CaryXiao1/cs140e-lightsaber/i2c/mpu-6050.c

// engler: simplistic mpu6050 driver code.
//
// we smash all the code in here so its easy to find in the lab
// setting: when it works, seperate it out!
//
// three parts:
//  1. i2c helpers (you don't have to modify)
//  2. accel routines (you have to finish)
//  3. gyro routines (you have to finish)
//
// two algorithms: 
//   - implement the code from scratch (fun! let us know you're
//     doing)
//   - grep for TODO and fill in.
//
// KEY: document why you are doing what you are doing.
//  **** put page numbers for any device-specific things you do ***
//  **** put page numbers for any device-specific things you do ***
//  **** put page numbers for any device-specific things you do ***
//  **** put page numbers for any device-specific things you do ***
//  **** put page numbers for any device-specific things you do ***
//  **** put page numbers for any device-specific things you do ***
//  **** put page numbers for any device-specific things you do ***
// 
// also: a sentence or two will go a long way in a year when you want 
// to re-use the code.
#include "rpi.h"
#include "mpu-6050.h"

/**********************************************************************
 * 1. i2c helpers (see i2c.h)  for reading and write individual registers,
 * and for doing burst reads of N registers.
 *
 * recall: each register has a 1 byte name and a 1 byte value.  we
 * read or write them explicitly using i2c rather than using memory
 * loads and stores (as we do with broadcom memory mapped device 
 * interfaces).
 *
 * you don't have to modify this.
 */

// read a single device register <reg> from i2c device 
// <addr> and return the result.
uint8_t imu_rd(uint8_t addr, uint8_t reg) {
    i2c_write(addr, &reg, 1);
    uint8_t v;
    i2c_read(addr,  &v, 1);
    return v;
}

// set a single device register <reg> on device
// <addr> to value <v>
// 
// the operation is sent over i2c as two 8-bit values: 
// (byte 0 = <reg>, byte 1 = <v>)
void imu_wr(uint8_t addr, uint8_t reg, uint8_t v) {
    uint8_t data[2];
    data[0] = reg;
    data[1] = v;
    i2c_write(addr, data, 2);
}

// do a "burst read" of <n> registers into buffer <v>, where 
//  - <addr> = device addr
//  - <base_reg> = lowest reg in sequence
//  - <n> = total number of 8-bit registers to read.
int imu_rd_n(uint8_t addr, uint8_t base_reg, uint8_t *v, uint32_t n) {
    i2c_write(addr, (void*) &base_reg, 1);
    return i2c_read(addr, v, n);
}

/**********************************************************************
 * 2. simple accel setup and use
 */

// IMU + accel register map
enum {
    // p6, p14
    accel_config_reg = 0x1c,
    accel_off = 3,

    USER_CTRL = 0x6a,   // p 39

    // p31,32
    ACCEL_XOUT_H = 0x3b,
    accel_xout_l = 0x3c,
    accel_yout_h = 0x3d,
    accel_yout_l = 0x3e,
    accel_zout_h = 0x3f,
    accel_zout_l = 0x40,

    // p 41
    PWR_MGMT_1 = 0x6b,
    // p 42
    PWR_MGMT_2 = 108,

    // p 29
    INT_STATUS = 0x3a,
    // p 28
    INT_ENABLE = 0x38,

    // NOTE: p 27, for interrupts
    INT_PIN_CFG = 0x37, 
};

// returns a scaled milligauss value given the
// scale that <g> can range over.
static int mg_scaled(int v, int g) {
    return (v * 1000 * g) / SHRT_MAX;
}

// takes in raw data and scales it.
imu_xyz_t accel_scale(accel_t *h, imu_xyz_t xyz) {
    int g = h->g;
    int x = mg_scaled(h->g, xyz.x);
    int y = mg_scaled(h->g, xyz.y);
    int z = mg_scaled(h->g, xyz.z);
    return xyz_mk(x,y,z);
}

// check interrupt status (INT_STATUS) to see 
// if data is ready.
// 
// extension: hook up gpio interrupts and 
// pull the reading into a circular buffer
// (similar to device lab).
int accel_has_data(const accel_t *h) {
    // pg. 29 of reg map, see DATA_RDY_INT at bit 0
    char reg = imu_rd(h->addr, INT_STATUS);
    return bit_is_on(reg, 0);
}


// combines a 8-bit <lo> and 8-bit <hi> from the sensor into
// a single *signed* 16-bit value.  you want to make sure that
// if the 16-th bit is set, the returned value will be negative.
// i'd suggest playing w/ gdb or small C programs to see that what
// C does matches your intuition.
static short mg_raw(uint8_t lo, uint8_t hi) {
    short out = 0; 
    out |= lo; 
    out |= hi << 8; 
    return out;
}

// sanity testing code.
static void test_mg(int expected, uint8_t l, uint8_t h, unsigned g) {
    int s_i = mg_scaled(mg_raw(h,l),g);

    output("expect = %d, got %d", expected, s_i);
    if(expected == s_i)
        output("success!\n");
    else
        output("failed!\n");

    assert(s_i == expected);
}
    
// set to accel 2g (p14), bandwidth 20hz (p15)
// https://stackoverflow.com/questions/60419390/mpu-6050-correctly-reading-data-from-the-fifo-register
    accel_t mpu6050_accel_init(uint8_t addr, unsigned accel_g) {
        unsigned g = 0;
    switch(accel_g) {
    case accel_2g: g = 2; break;
    case accel_4g: g = 4; break;
    case accel_8g: g = 8; break;
    case accel_16g: g = 16; break;
    default: panic("invalid g=%b\n", g);
    }

    // first test that your scaling works.
    // this is device independent.
    test_mg(0, 0x00, 0x00, 2);
    test_mg(350, 0x16, 0x69, 2);
    test_mg(1000, 0x40, 0x09, 2);
    test_mg(-350, 0xe9, 0x97, 2);
    test_mg(-1000, 0xbf, 0xf7, 2);

    // initialized your accel to 2g (accel_confi_reg)
    uint8_t accel_config = imu_rd(addr, accel_config_reg); 
    accel_config &= ~(0b11 << 3); 
    // accel_config = bits_set(accel_config, 3, 4, accel_g);  
    imu_wr(addr, accel_config_reg, accel_config);
    // todo("setup accel with 2g");

    output("accel_config_reg=%b\n", imu_rd(addr, accel_config_reg));
    return (accel_t) { .addr = addr, .g = g, .hz = 20 };
}

// hard reset: recall --- for all external devices connected to 3v or 
// 5v, rebooting the pi has no effect on the external device.  so either
// we would have to disconnect/reconnect the power (manually or w/ some
// transistor) or we can use the device control to do a hard reset.  we
// do the latter.
void mpu6050_reset(uint8_t addr) {
    // make sure device is up.
    delay_ms(100);

    // page 41: to reset device: set bit 7 = 1 in register
    // PWR_MGMT_1 (register 0x6b)
    // todo("reset device");
    uint8_t pwr_mgmt_reg = imu_rd(addr, PWR_MGMT_1); 
    pwr_mgmt_reg = pwr_mgmt_reg | (1 << 7); // page 42; resets all internal registers to default values
    imu_wr(addr, PWR_MGMT_1, pwr_mgmt_reg); 

    // TODO: See Section 3 for default values

    // XXX: we should read different registers and see that they
    // went back to startup.

    // give time to shutdown, spin up.
    delay_ms(100);

    if(bit_is_on(imu_rd(addr, PWR_MGMT_1), 6))
        output("device booted up in sleep mode!\n");

    // clear sleep mode: (PWR_MGMT_1)
    // if you do *NOT* do this, then the device we have does not work.
    // according to my reading of the data sheet, the value of 0x6b should
    // be 0 after reset.  so i don't get this.
    // todo("clear sleep mode");
    pwr_mgmt_reg = imu_rd(addr, PWR_MGMT_1); // Had to read again
    pwr_mgmt_reg = bit_clr(pwr_mgmt_reg, 6); // pg. 42
    imu_wr(addr, PWR_MGMT_1, pwr_mgmt_reg); // put back in memory

    delay_ms(100);

    // page 39: USER_CTRL (register 0x6a): reset:
    //   - the signal path 
    //   - i2c master mode 
    //   - fifo
    // not sure if redundant after device reset --- datasheet
    // unclear --- so we do to be sure.
    // todo("reset all these");
    uint8_t usr_ctrl_reg = imu_rd(addr, USER_CTRL); 
    usr_ctrl_reg = bits_set(usr_ctrl_reg, 0, 2, 0b111); // the signal path
    imu_wr(addr, USER_CTRL, usr_ctrl_reg); 

    delay_ms(100);

    // NOTE: enable interrupts only on the IMU, not on your pi.
    // (INT_ENABLE) after you config (p27):
    // - latch to be held high until cleared;
    // - read to clear it.
    uint8_t int_pin_cfg_reg = imu_rd(addr, INT_PIN_CFG); 
    int_pin_cfg_reg = bit_set(int_pin_cfg_reg, 4); 
    int_pin_cfg_reg = bit_set(int_pin_cfg_reg, 5); // NOTE: questionable
    imu_wr(addr, INT_PIN_CFG, int_pin_cfg_reg); 

    uint8_t int_enable_reg = imu_rd(addr, INT_ENABLE); 
    int_enable_reg = bit_set(int_enable_reg, 0);  // data ready interrupt
    // int_enable_reg = bit_set(int_enable_reg, 3); 
    // int_enable_reg = bit_set(int_enable_reg, 4); 
    // int_enable_reg = bit_set(int_enable_reg, 6); 
    imu_wr(addr, INT_ENABLE, int_enable_reg); 
    // todo("enable IMU interrupts so you can tell that data is ready");
}

// block until there is data and then return it (raw)
//
// p26 interprets the data.
// if high bit is set, then result is negative.
//
// read them all at once for consistent
// readings using autoincrement.
imu_xyz_t accel_rd(const accel_t *h) {
    uint8_t addr = h->addr;
    uint8_t regs[6];

    // wait until data.
    while(!accel_has_data(h))
        ;

    // read in from the IMU using imu_rd_n.
    //
    // NOTE: from page 32: the "high" byte has a register 
    // value *smaller than* the "low" byte.
    //
    //      xout[15:8] = 0x3b
    //      xout[7:0]  = 0x3c
    //      yout[15:8] = 0x3d
    //      yout[7:0]  = 0x3e
    //      zout[15:8] = 0x3f
    //      zout[7:0]  = 0x40

    // return a raw xyz point.
    int x =  0;
    int y =  0;
    int z =  0;

    // NOTE:
    //  - if this doesn't work, read regs one at a time.
    //  - you'll have to comine the two 8-bit unsigned
    //    regs into a signed 16 bit number using <mg_raw>
    uint8_t v[6]; 
    imu_rd_n(addr, ACCEL_XOUT_H, v, 6);
    
    // combine to get values
    x = mg_raw(v[1], v[0]); 
    y = mg_raw(v[3], v[2]); 
    z = mg_raw(v[5], v[4]); 
    // todo("implement burst reads and return as unscaled x,y,z");
    
    return xyz_mk(x,y,z);
}

/*********************************************************************
 * gyro code
 * 
 * don't trust the scaling  code.
 */

// gyro registers.
enum {
    // p13, p6
    CONFIG = 28, 
    // p14, p6
    GYRO_CONFIG = 29, 

    // p6, p14
    gyro_config_reg = 0x1b,

    // p7
    GYRO_XOUT_H = 67,
};

static inline int 
mdps_scaled(int x, int dps_scale) {
    return (x * dps_scale) / 1000;
}

// not sure this is right: use the code below?
imu_xyz_t gyro_scale(gyro_t *h, imu_xyz_t xyz) {
    int dps = h->dps;
    int x = mdps_scaled(dps, xyz.x);
    int y = mdps_scaled(dps, xyz.y);
    int z = mdps_scaled(dps, xyz.z);
    return xyz_mk(x,y,z);
}

// not sure this is right.
static int dps_to_scale(unsigned dps) {
    switch(dps) {
    // we do this just for testing.
    case 245:
    case 250:  return  8750;
    case 500:  return 17500;
    case 1000: return 35000;
    case 2000: return 70000;
    default: panic("invalid dps: %d\n", dps);
    }
}

// not sure this is right.
static int mdps_scale_deg2(int deg, int dps) {
    // hack to get around no div
    if(dps == 250)
        return (deg * 250) / SHRT_MAX;
    else if(dps == 500)
        return (deg * 500) / SHRT_MAX;
    else
        panic("bad dps=%d\n", dps);
}

// not sure this is right.
static int mdps_scale_deg(int deg, int dps) {
    return (deg * dps_to_scale(dps)) /1000;
}

static inline int within(int exp, int have, int tol) {
    int diff = exp - have;
    if(diff < 0)
        diff = -diff;
    return diff <= tol;
}

static void test_dps(int expected_i, uint8_t h, uint8_t l, int dps) {
    int s_i = mdps_scale_deg(mg_raw(l, h), dps);
    expected_i *= 1000;
    int tol = 5;
    if(!within(expected_i, s_i, tol))
        panic("expected %d, got = %d, scale=%d\n", expected_i, s_i, dps);
    else
        output("expected %d, got = %d, (within +/-%d) scale=%d\n", expected_i, s_i, tol, dps);
}

gyro_t mpu6050_gyro_init(uint8_t addr, unsigned gyro_dps) { 
    // device independent testing.
    unsigned dps = 245;
    test_dps(0, 0x00, 0x00, dps);
    test_dps(100, 0x2c, 0xa4, dps);
    test_dps(200, 0x59, 0x49, dps);
    test_dps(-100, 0xd3, 0x5c, dps);

    dps = 0;
    switch(gyro_dps) {
    case gyro_250dps:   dps = 250; break;
    case gyro_500dps:   dps = 500; break;
    case gyro_1000dps:  dps = 1000; break;
    case gyro_2000dps:  dps = 2000; break;
    default: panic("invalid dps: %b\n", dps);
    }

    // you'll need to set CONFIG (p13) and GYRO_CONFIG (p14)
    // todo("initialize the gyro");
    uint8_t reg = imu_rd(addr, GYRO_CONFIG); 
    reg = bits_set(reg, 3, 4, gyro_dps); 
    // accel_config = bits_set(accel_config, 3, 4, accel_g);  
    imu_wr(addr, GYRO_CONFIG, reg);
    
    return (gyro_t) { .addr = addr, .dps = dps,  };
}

// use int or fifo to tell when data.
int gyro_has_data(const gyro_t *h) {
    uint8_t int_status_register = imu_rd(h->addr, INT_STATUS);
    return bit_is_on(int_status_register, 0); 
    // todo("implement this");
}

// return a single raw gyro reading.
imu_xyz_t gyro_rd(const gyro_t *h) {
    // not sure if we have to drain the queue if there are more readings?

    unsigned dps_scale = h->dps;
    uint8_t addr = h->addr;

    while(!gyro_has_data(h))
        ;

    int x=0,y=0,z=0;

    // you'll need to combine the 8-bit regs into a 16-bit using <mg_raw>
    // todo("implement this");
    uint8_t v[6]; 
    imu_rd_n(addr, GYRO_XOUT_H, v, 6);
    
    // combine to get values
    x = mg_raw(v[1], v[0]); 
    y = mg_raw(v[3], v[2]); 
    z = mg_raw(v[5], v[4]); 
    return xyz_mk(x,y,z);
}
