CaryXiao1/cs140e-lightsaber/pwm/pwm.h

#ifndef PWM_H
#define PWM_H

#include "rpi.h"

/*
 * generate a square wave with the given frequency.
 */
void play_tone(int freq);

/*
 * Hardware abstractions for pulse width modulation (PWM) of
 * digital signals.
 *
 * Author: Pat Hanrahan <hanrahan@cs.stanford.edu>
 * Date: Feb 15, 2016
 */

/*
 * Initialize the pwm module. 
 */
void pwm_init(void);


/*
 * Assumes we already called audio init, change the sample rate
 *
 */
void set_sample_rate(int sample_rate);


void audio_init(int sample_rate);

/*
 * Set the PWM clock frequency.
 *
 * @param frequency      the frequency of the PWM clock
*/
void pwm_set_clock(int frequency);

/*
 * Set the PWM mode.
 *
 * @param chan      the PWM channel - either 0 or 1
 * @param markspace use PWM_MARKSPACE mode or PWM_SIGMADELTA mode
 */
#define PWM_SIGMADELTA 0
#define PWM_MARKSPACE  1
void pwm_set_mode(int chan, int markspace);

/*
 * Set the PWM fifo..
 *
 * @param chan      the PWM channel - either 0 or 1
 * @param usefifo   usefifo or not
 */
void pwm_set_fifo(int chan, int usefifo);
void pwm_clear_fifo(void);

/*
 * Enable or disable PWM.
 *
 * @param chan      the PWM channel - either 0 or 1
 */
void pwm_enable(int chan);
void pwm_disable(int chan);

/*
 * Set the PWM range for the given channel
 *
 * @param chan      the PWM channel - either 0 or 1
 * @param range     range (typically between 0 and 4095)
 */
void pwm_set_range(int chan, int range);

/*
 * Set the PWM width for the given channel
 *
 * @param chan      the PWM channel - either 0 or 1
 * @param width     width (typically between 0 and 4095). A width of range/2
 *                  corresponds to a 50% duty cycle.
 */
void pwm_set_width(int chan, int width);

/*
 * Write a value to all channels
 *
 * @param value     value (typically between 0 and 4095). Set the PWM width 
 *                  to value.
 */
void pwm_write(int value);

/*
 * Read the current status of the PWM channel.
 *
 * @return the current status of the channels. If PWM_FULL1 is set, then
 * need to wait until the channel is not full before writing a new value.
 */
#define PWM_FULL1 0x01
unsigned int pwm_get_status(void);

#endif
