CaryXiao1/cs140e-lightsaber/neopixel/code/WS2812B.h

#ifndef __WS2812B__
#define __WS2812B__
/*
 * engler: possible interface fo ws2812b light strip, cs240lx
 *
 * the low-level "driver" code for the WS2812B addressable LED light strip.  
 *      Datasheet in docs/WS2812B
 *
 * the higher level support stuff is in neopix.c
 * 
 * Key sentence  missing from most documents:
 *	Addressing is indirect: you don’t pass a NeoPixel’s address
 *	via SPI. Instead the order of data in the frame provides the
 *	addressing: the first three color values are taken by the first
 *	NeoPixel in line, the second set of values by the next NeoPixel,
 *	the third by the third and so on.
 *		--- https://developer.electricimp.com/resources/neopixels
 *
 * 	I.e., it's not a FIFO buffer, the first thing you write gets claimed
 *	by the first LED, etc.
 * 
 * to send a:
 *	- 0 = T0H, T0L
 * 	- 1 = T1H, T1L
 * 	- FLUSH = how long to wait with voltage low to flush it out.
 *
 * One way to communicate more information with a device is to use a fancier
 * protocol (e.g., SPI, I2C).  A simpler hack is to use time --- there's a lot 
 * of information you can encode in various numbers of nanoseconds.    
 *
 * The WS2812B uses time as follows:
 *      To send a 1 bit: write a 1 for T1H, then a 0 for T0H.
 *      To send a 0 bit: write a 1 for T1L, then a 0 for T0L.
 *
 * The protocol:
 *   - Each pixel needs 3 bytes of information (G,R,B) [in that order] for the color.  
 *   - The first 3 bytes you sent get claimed by the first pixel, the second 3 bytes 
 *     by the second, and so forth.
 *   - You then hold the communication pin low for FLUSH cycles to tell the pixel you
 *        are done.
 *  
 * The data sheet for WS2812B says the following timings: 
 *      T0H    0: .35us +- .15us
 *      T1H    1: .9us +- .15us
 *      T0L    0: .9us +- .15us
 *      T1L    1: .35us +- .15us
 *      Trst = 80us 
 *
 *  The above timings work. However, for long light strings, they can consume significant
 *  time.   Ideally we'd like to push the times as low as possible so that we can set/unset
 *  more pixels per second.   The following *seem* to work on the light strings I have,
 *  but could break on others (or could break on mine with the wrong set of pixels).   Use
 *  with caution:
 *      T0H = 200ns + eps
 *      T1H = 750ns + eps
 *      T0L = 750ns + eps
 *      T1L = 200ns + eps
 */
#include "cycle-count.h"

// A+ CPU speed: 700MHz (700 million cycles per second)
#define MHz 700UL

// convert nanoseconds to pi cycles: you need to modify this if you change
// the pi's clock speed.
#define ns_to_cycles(x) (unsigned) ((x * 7UL) / 10UL )


#ifndef OPTIMIZE_NEO_TIMING

// #   error "you need to define these enums using the datasheet."

    // these are the timings recommended by the datasheet.
    // if you optimize, i would suggest making a seperate copy you 
    // can flip between.
    enum { 
        // to send a 1: set pin high for T1H ns, then low for T0H ns.
        T1H = ns_to_cycles(900),        // Width of a 1 bit in ns
        T0H = ns_to_cycles(350),        // Width of a 0 bit in ns
        // to send a 0: set pin high for T1L ns, then low for T0L ns.
        T1L = ns_to_cycles(350),        // Width of a 1 bit in ns
        T0L = ns_to_cycles(900),        // Width of a 0 bit in ns

        // to make the LED switch to the new values, hold the pin low for FLUSH ns
        FLUSH = ns_to_cycles(50 *1000)    // how long to hold low to flush
    };

#else

    // the serial, time-based WS2812B protocl has the downside that everything is 
    // (obviously) O(n) based on the number of pixels --- the longer the delays for
    // each pixel, the slower we can make changes.   so we sleazily cut down the 
    // delays to the lowest that seem to consistently work.  for a long
    // light strip this might add up.

    // put your optimized enums here.

#endif

/****************************************************************************
 * Support code.  We put this first so it can be inlined.
 *
 * You should modify these.
 */

// defines the pi-specific code to read its cycle-counter.
#include "cycle-count.h"

// make sure we don't call the non-inlined gpio implementations.
#define gpio_set_on "error"
#define gpio_set_off "error"
#define gpio_write "error"

enum {
    GPIO_BASE = 0x20200000,
    gpio_set0  = (GPIO_BASE + 0x1C),
    gpio_clr0  = (GPIO_BASE + 0x28),
    gpio_set1  = gpio_set0 + 4,
    gpio_clr1  = gpio_clr0 + 4,
    gpio_lev0  = (GPIO_BASE + 0x34), 
    gppud = (GPIO_BASE + 0x94),
    gppudclk0 = (GPIO_BASE + 0x98), 
};

// duplicate set_on/off so we can inline to reduce overhead.
// they have to run in < the delay we are shooting for.
static inline void gpio_set_on_raw(unsigned pin) {
    // use <gpio_set0>
    // volatile cast then de-reference
    // if (pin == 47) { 
    //     *(volatile uint32_t*)(gpio_set1) = (1 << (pin - 32)); 
    // } else {
    *(volatile uint32_t*)gpio_set0 = 1 << pin; 
    // }
}

static inline void gpio_set_off_raw(unsigned pin) {
    // use <gpio_set0>
    // volatile cast then de-reference
    // if (pin == 47) { 
    //     *(volatile uint32_t*)gpio_clr1 = (1 << (pin - 32)); 
    // } else {
    *(volatile uint32_t*)gpio_clr0 = 1 << pin; 
    // }
}

// use cycle_cnt_read() to delay <n_cyc> cycles measured from <start_cyc>
static inline void delay_ncycles(unsigned start_cyc, unsigned n_cyc) {
    n_cyc += start_cyc;
    while (cycle_cnt_read() <= n_cyc)
        ; 
}


/****************************************************************************
 * The entire WS2812B protocol: you will write this code.
 *
 * We inline everything to (hopefully) minimize issues meeting our time budgets.
 * Note: Make sure to put function definitions before uses.
 *
 * You can replace these prototypes with your own functions if you want.  These
 * are just some mild suggestions.
 */

// we inline, so don't think is necessary.  code seems to have runtime variance
// depending on its alignment.  Can experiment if need be.
// #pragma GCC optimize ("align-functions=16")

static unsigned const compensation = 16;

// two helpers for implementing T1H,T0H,T0L,T1L

// write 1 for <ncycles>: since reading the cycle counter itself takes cycles
// you may need to add a constant to correct for this.
static inline void write_1(unsigned pin, unsigned ncycles) {
    // use gpio_set_on_raw
    // Write a 1 for T1H nanoseconds -- how to wait for time
    unsigned start = cycle_cnt_read(); 
    gpio_set_on_raw(pin);
    delay_ncycles(start, ncycles); 
}

// write 0 for <ncycles>: since reading the cycle counter takes cycles you
// may need to add a constant to correct for it.
static inline void write_0(unsigned pin, unsigned ncycles) {
    // use gpio_set_off_raw
    unsigned start = cycle_cnt_read(); 
    gpio_set_off_raw(pin); 
    delay_ncycles(start, ncycles); 
}

// implement T1H from the datasheet (call write_1 with the right delay)
static inline void t1h(unsigned pin) {
    write_1(pin, T1H-10); // Write 1 with T1H delay
}

// implement T0H from the datasheet (call write_0 with the right delay)
static inline void t0h(unsigned pin) {
    write_1(pin, T0H-10); // write 0 with T0H delay
}
// implement T1L from the datasheet.
static inline void t1l(unsigned pin) {
    write_0(pin, T1L-30); 
}
// implement T0L from the datasheed.
static inline void t0l(unsigned pin) {
    write_0(pin, T0L-20); 
}
// implement RESET from the datasheet.
static inline void treset(unsigned pin) {
    write_0(pin, FLUSH-10); 
}

/***********************************************************************************
 * public functions.
 */

// flush out the pixels.
static inline void pix_flush(unsigned pin) { 
    treset(pin); 
}

// transmit a {0,1} bit to the ws2812b
static inline void pix_sendbit(unsigned pin, uint8_t b) {
    if (b) { // b == 1
        t1h(pin); 
        t1l(pin); 
    } else { // b == 0
        t0h(pin); 
        t0l(pin); 
    }
}

// use pix_sendbit to send byte <b>
//
// XXX: it might seem sensible to unroll this code.  however with all the inlining it 
// becomes huge: unclear if better.  if you decide to inline it, make sure you run
// tests before and after.  
static void pix_sendbyte(unsigned pin, uint8_t b) {
    for (int i = 7; i >= 0; i--) {
        pix_sendbit(pin, (b >> i) & 1);
    }
    // unimplemented();
}

// use pix_sendbyte to send bytes [<r> red, <g> green, <b> blue out on pin <pin>.
static inline void pix_sendpixel(unsigned pin, uint8_t r, uint8_t g, uint8_t b) {
    // XXX: b/c sendbyte is not inlined, coulde lead to a non-trivial
    // delay between the send bytes --- when you optimize it's possible you need 
    // to trim the delays you use.
    // use pix_sendbyte to send <r>, <g> <b>
    pix_sendbyte(pin, r); 
    pix_sendbyte(pin, g); 
    pix_sendbyte(pin, b); 
    // unimplemented();
    
}
#endif
