CaryXiao1/cs140e-lightsaber/nrf-bootloader/2-pi-side/nrf-test.h

#ifndef __NRF_TEST_H__
#define __NRF_TEST_H__
// various support routines for testing.  
#include "rpi.h"
#include "nrf.h"

// left side NRF pin-out of parthiv's board (server)
// static inline nrf_conf_t
// parthiv_left(uint32_t nbytes, uint32_t ch) {
//     nrf_conf_t c = nrf_conf_mk(nbytes, ch);
//     c.spi_chip = 0;
//     c.ce_pin = 25; // used to be 6; we moved the CE pin specifically on the lightsaber!
//     c.int_pin = 22;
//     return c;
// }

// right side NRF pin-out of parthiv's board (client)
static inline nrf_conf_t
parthiv_right(uint32_t nbytes, uint32_t ch) {
    nrf_conf_t c = nrf_conf_mk(nbytes, ch);
    c.spi_chip = 1;
    c.ce_pin = 5;
    c.int_pin = 23;
    return c;
}

static inline nrf_conf_t
client_conf(uint32_t nbytes) {
    return parthiv_right(nbytes,nrf_default_channel);
}
// static inline nrf_conf_t
// server_conf(uint32_t nbytes) {
//     return parthiv_left(nbytes,nrf_default_channel);
// }

// server wrappers for making an nrf: <ack_p> indicates ack'd or not.
// static inline nrf_t *
// server_mk(uint32_t rxaddr, uint32_t nbytes, int ack_p) {
//     return nrf_init(server_conf(nbytes), rxaddr, ack_p);
// }
// static inline nrf_t *
// server_mk_ack(uint32_t rxaddr, uint32_t nbytes) {
//     return server_mk(rxaddr, nbytes, 1);
// }
// static inline nrf_t *
// server_mk_noack(uint32_t rxaddr, uint32_t nbytes) {
//     return server_mk(rxaddr, nbytes, 0);
// }

// client wrappers.
static inline nrf_t *
client_mk(uint32_t rxaddr, uint32_t nbytes, int ack_p) {
    return nrf_init(client_conf(nbytes), rxaddr, ack_p);
}
static inline nrf_t *
client_mk_ack(uint32_t rxaddr, uint32_t nbytes) {
    return client_mk(rxaddr, nbytes, 1);
}
static inline nrf_t *
client_mk_noack(uint32_t rxaddr, uint32_t nbytes) {
    return client_mk(rxaddr, nbytes, 0);
}
#endif
